TeFka/PeatMonitoringProject/EmbeddedSoftware/CombinedSystems/stmChild/Core/Inc/retarget.h

/*
 * retarget.h
 *
 *  Created on: Feb 15, 2023
 *      Author: Admin
 */

#ifndef INC_RETARGET_H_
#define INC_RETARGET_H_

#include "stm32l4xx_hal.h"
#include <sys/stat.h>

void RetargetInit(UART_HandleTypeDef *huart);
int _isatty(int fd);
int _write(int fd, char* ptr, int len);
int _close(int fd);
int _lseek(int fd, int ptr, int dir);
int _read(int fd, char* ptr, int len);
int _fstat(int fd, struct stat* st);

#endif /* INC_RETARGET_H_ */
